pablomayobre/Risem/PC Software/Main/collisions.lua

local chu = function (st)
	if st == "gpredict" then
		return "manual"
	elseif st == "manual" then
		return "gpredict"
	end
end
local collisions = {
	ROTOR = function (x,y,states)
		if x > 70 and y > 41 and x < 134 and y < 62 then
			states.ROTORSTATE = chu(states.ROTORSTATE)
		end
	end,
	RADIO = function (x,y,states)
		if x > 209 and y > 41 and x < 273 and y < 62 then
			states.RADIOSTATE = chu(states.RADIOSTATE)
		end
	end,
	ARROWSAZ = function (x,y,states)
		if states.ROTORSTATE == "manual" then
			if y > 88 and y < 100 then
				local total = tonumber(table.concat(states.AZ))/10
				if total < 360 then
					if x > 32 and x < 55 then
						somethingchanged = true
						if total + 100 <= 360 then
							states.AZ[1] = states.AZ[1] + 1
						end
					elseif x > 69 and x < 92 then
						somethingchanged = true
						if total + 10 <= 360 then
							states.AZ[2] = states.AZ[2] + 1
						end					
					elseif x > 106 and x < 129 then
						somethingchanged = true
						if total + 1 <= 360 then
							states.AZ[3] = states.AZ[3] + 1
						end	
					elseif x > 157 and x < 180 then
						somethingchanged = true
						if total + .1 <= 360 then
							states.AZ[4] = states.AZ[4] + 1
						end	
					end
					if states.AZ[4] > 9 then
						states.AZ[4] = 0
						states.AZ[3] = states.AZ[3] + 1
					end
					if states.AZ[3] > 9 then
						states.AZ[3] = 0
						states.AZ[2] = states.AZ[2] + 1
					end
					if states.AZ[2] > 9 then
						states.AZ[2] = 0
						states.AZ[1] = states.AZ[1] + 1
					end
				end
			elseif y > 156 and y < 168 then
				local total = tonumber(table.concat(states.AZ))/10
				if total > 0 then
					if x > 32 and x < 55 then
						somethingchanged = true
						if total - 100 >= 0 then
							states.AZ[1] = states.AZ[1] - 1
						end
					elseif x > 69 and x < 92 then
						somethingchanged = true
						if total - 10 >= 0 then
							states.AZ[2] = states.AZ[2] - 1
						end					
					elseif x > 106 and x < 129 then
						somethingchanged = true
						if total - 1 >= 0 then
							states.AZ[3] = states.AZ[3] - 1
						end	
					elseif x > 157 and x < 180 then
						somethingchanged = true
						if total - .1 >= 0 then
							states.AZ[4] = states.AZ[4] - 1
						end	
					end
					if states.AZ[4] < 0 then
						states.AZ[4] = 9
						states.AZ[3] = states.AZ[3] - 1
					end
					if states.AZ[3] < 0 then
						states.AZ[3] = 9
						states.AZ[2] = states.AZ[2] - 1
					end
					if states.AZ[2] < 0 then
						states.AZ[2] = 9
						states.AZ[1] = states.AZ[1] - 1
					end
				end
			end
		end
	end,
	ARROWSEL = function (x,y,states)
		if states.ROTORSTATE == "manual" then
			if y > 88 and y < 100 then
				local total = tonumber(table.concat(states.EL))/10
				if total < 90 then
					if x > 263 and x < 286 then
						somethingchanged = true
						if total + 10 <= 90 then
							states.EL[1] = states.EL[1] + 1
						end
					elseif x > 300 and x < 323 then
						somethingchanged = true
						if total + 1 <= 90 then
							states.EL[2] = states.EL[2] + 1
						end					
					elseif x > 351 and x < 374 then
						somethingchanged = true
						if total + .1 <= 90 then
							states.EL[3] = states.EL[3] + 1
						end	
					end
					if states.EL[3] > 9 then
						states.EL[3] = 0
						states.EL[2] = states.EL[2] + 1
					end
					if states.EL[2] > 9 then
						states.EL[2] = 0
						states.EL[1] = states.EL[1] + 1
					end
				end
			elseif y > 156 and y < 168 then
				local total = tonumber(table.concat(states.EL))/10
				if total > 0 then
					if x > 263 and x < 286 then
						somethingchanged = true
						if total - 10 >= 0 then
							states.EL[1] = states.EL[1] - 1
						end
					elseif x > 300 and x < 323 then
						somethingchanged = true
						if total - 1 >= 0 then
							states.EL[2] = states.EL[2] - 1
						end					
					elseif x > 351 and x < 374 then
						somethingchanged = true
						if total - .1 >= 0 then
							states.EL[3] = states.EL[3] - 1
						end	
					end
					if states.EL[3] < 0 then
						states.EL[3] = 9
						states.EL[2] = states.EL[2] - 1
					end
					if states.EL[2] < 0 then
						states.EL[2] = 9
						states.EL[1] = states.EL[1] - 1
					end
				end
			end
		end
	end,
	ARROWSFRUP = function (x,y,states)
		if states.RADIOSTATE == "manual" then
			if y > 205 and y < 217 then
				local total = tonumber(table.concat(states.FR))
				if total < 999999999 then
					if x > 32 and x < 55 then
						somethingchanged = true
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
					end
					if states.FR[6] < 0 then
						states.FR[6] = 9
						states.FR[5] = states.FR[5] - 1
					end
					if states.FR[5] < 0 then
						states.FR[5] = 9
						states.FR[4] = states.FR[4] - 1
					end
					if states.FR[4] < 0 then
						states.FR[4] = 9
						states.FR[3] = states.FR[3] - 1
					end
					if states.FR[3] < 0 then
						states.FR[3] = 9
						states.FR[2] = states.FR[2] - 1
					end
					if states.FR[2] < 0 then
						states.FR[2] = 9
						states.FR[1] = states.FR[1] - 1
					end
				end
			end
		end
	end,
	LOGO = function (x,y,states)
		local siz = 413*0.25
		if x > 446 and x < 446 + siz and y > 190 and y < 190 + siz then
			states.LOGO = states.LOGO + 1
		else
			states.LOGO = 0
		end
	end,
	CONFIG = function (x,y,states)
		if x > 505 and y > 6 and x < 535 and y < 26 then
			func.close()
		end
	end
}

return collisions
